lbrodie6/UofG_TDP3_TeamYes/hardware/photomasks/FRDMBoard_V2_Bottom.pdf

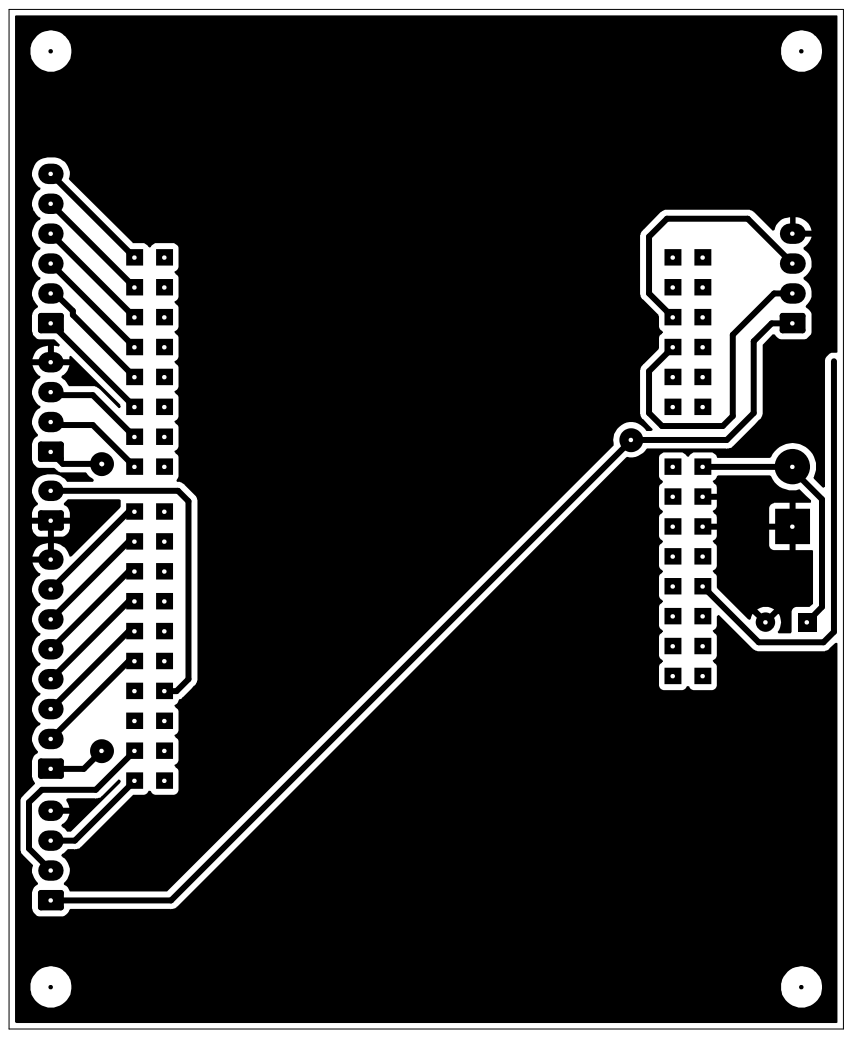
[picture p14: page 1]
