lbrodie6/UofG_TDP3_TeamYes/hardware/photomasks/FRDMBoard_V2_Top.pdf

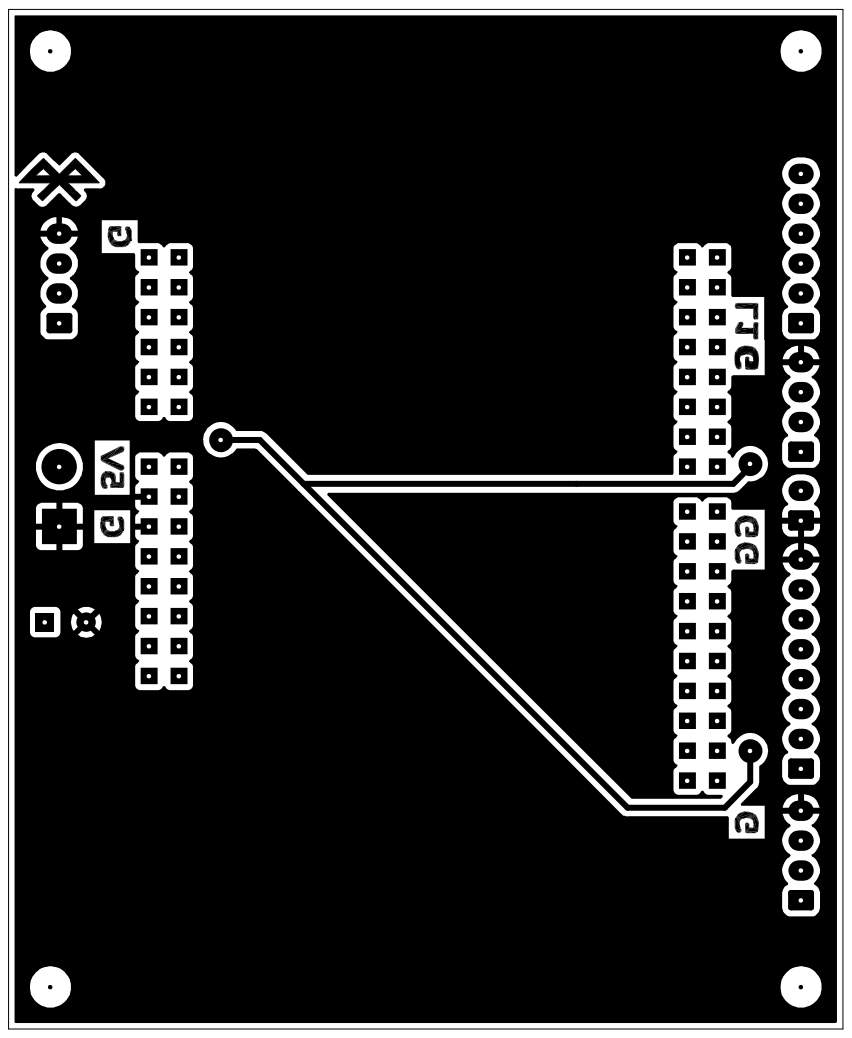
[picture p15: page 1]
