lbrodie6/UofG_TDP3_TeamYes/hardware/photomasks/ColourSensorBoard_V1_Bottom.pdf

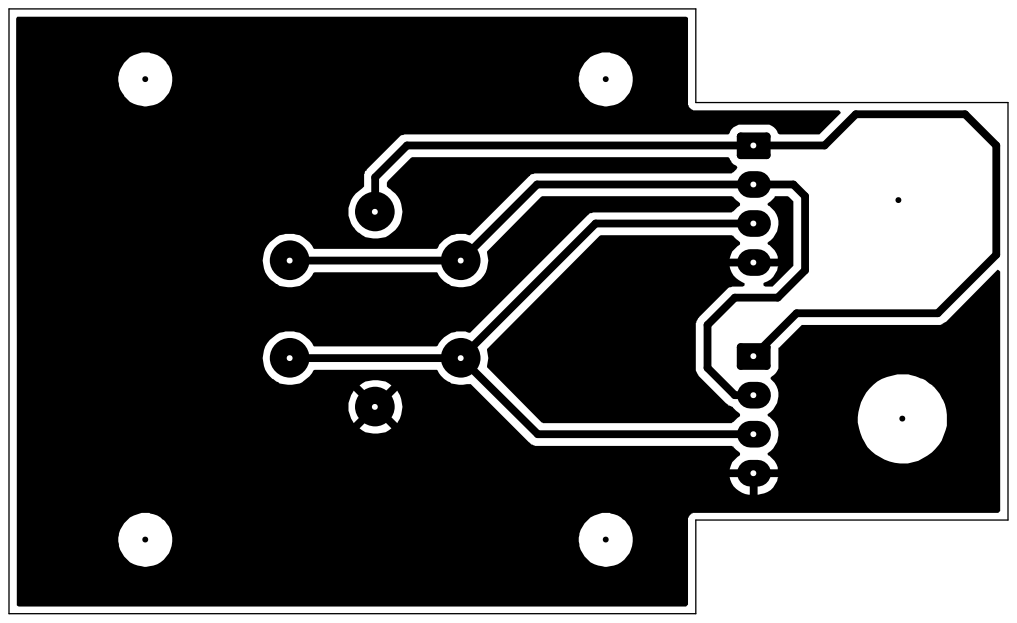
[picture p16: page 1]
