lbrodie6/UofG_TDP3_TeamYes/hardware/photomasks/ColourSensorBoard_V1_Top.pdf

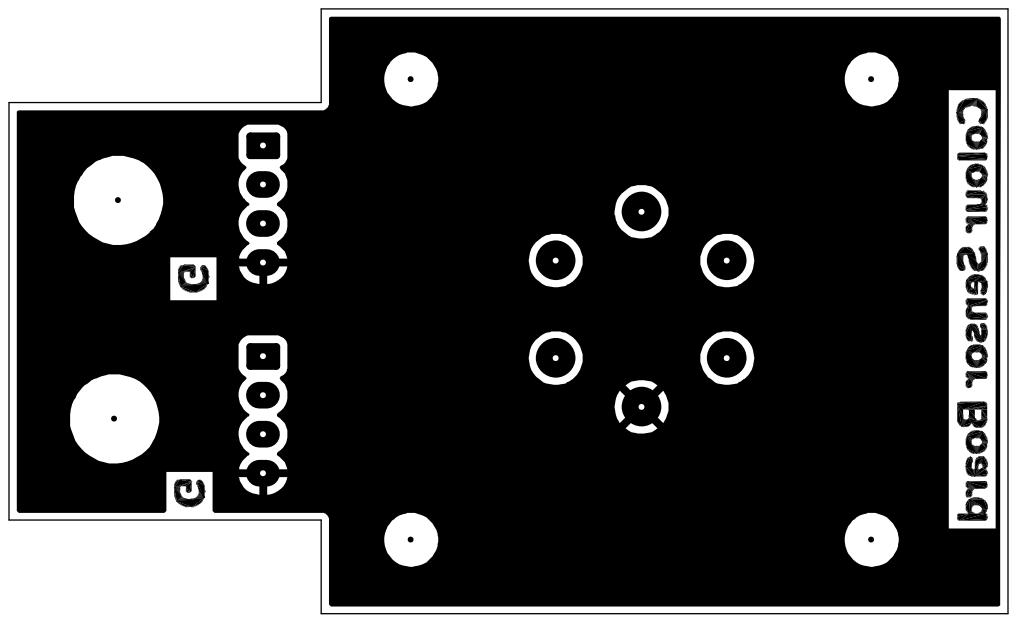
[picture p17: page 1]
