lbrodie6/UofG_TDP3_TeamYes/hardware/photomasks/FRDMBoard_V1_Bottom.pdf

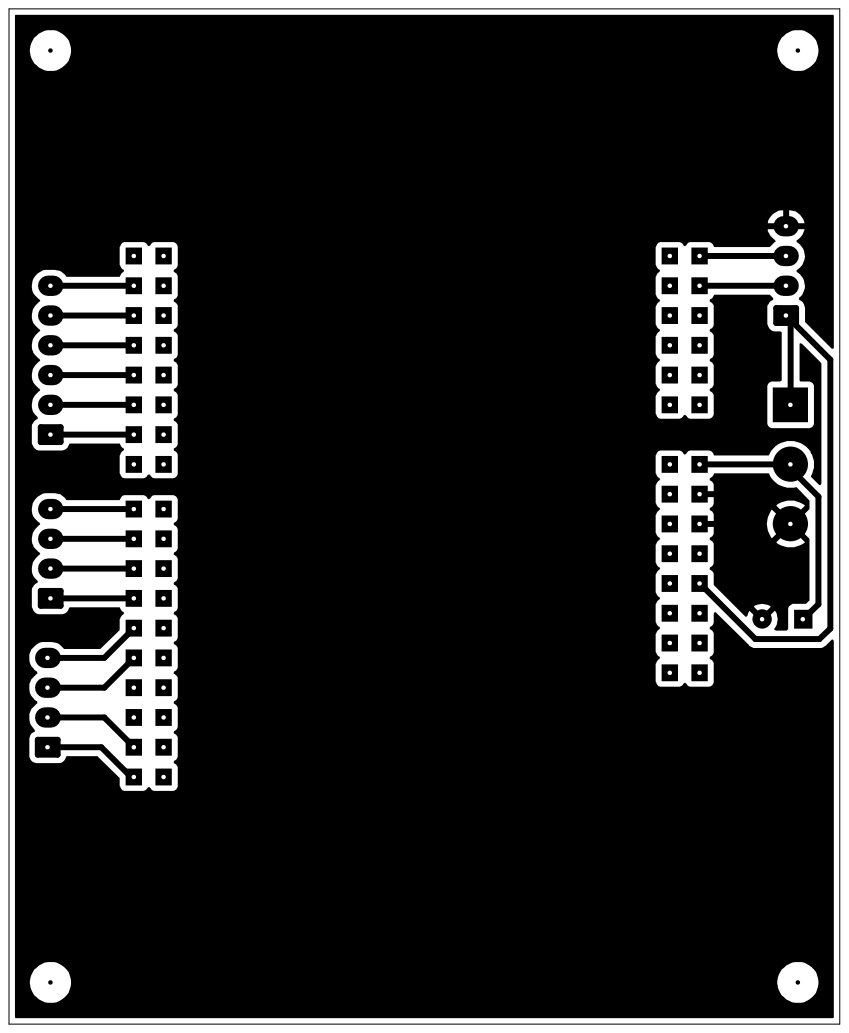
[picture p18: page 1]
