lbrodie6/UofG_TDP3_TeamYes/hardware/photomasks/FRDMBoard_V1_Top.pdf

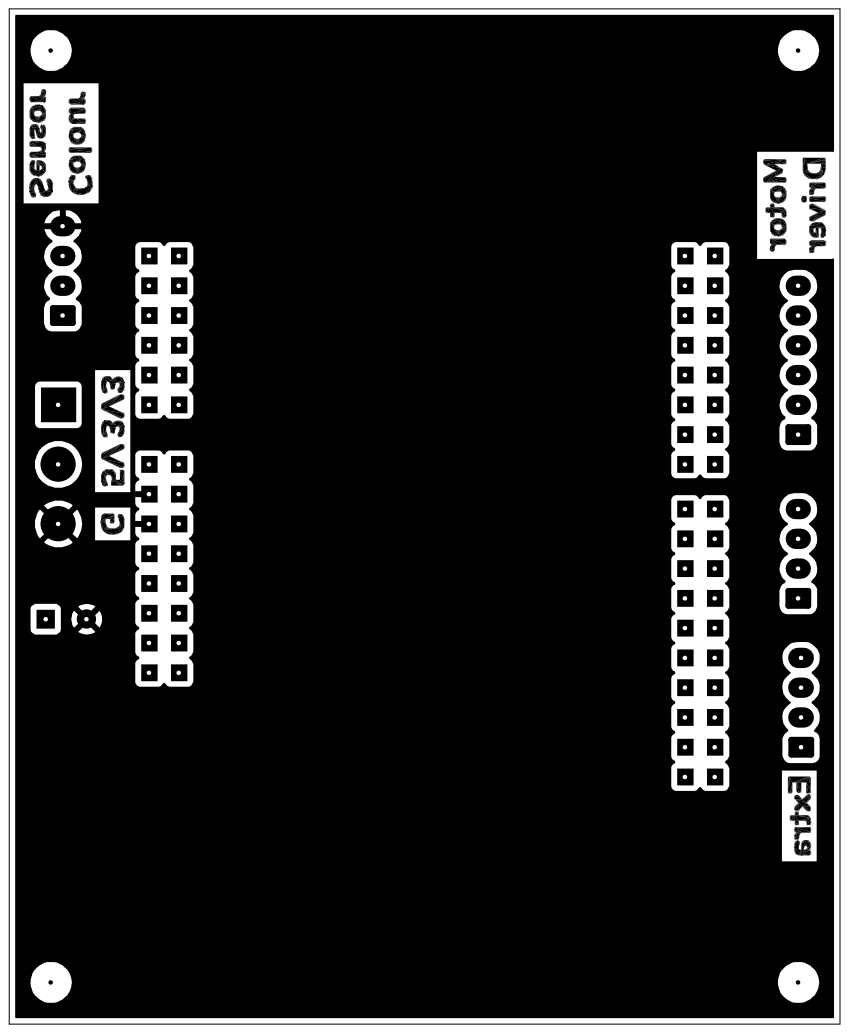
[picture p19: page 1]
