lbrodie6/UofG_TDP3_TeamYes/hardware/photomasks/MotorBoard_V1_Bottom.pdf

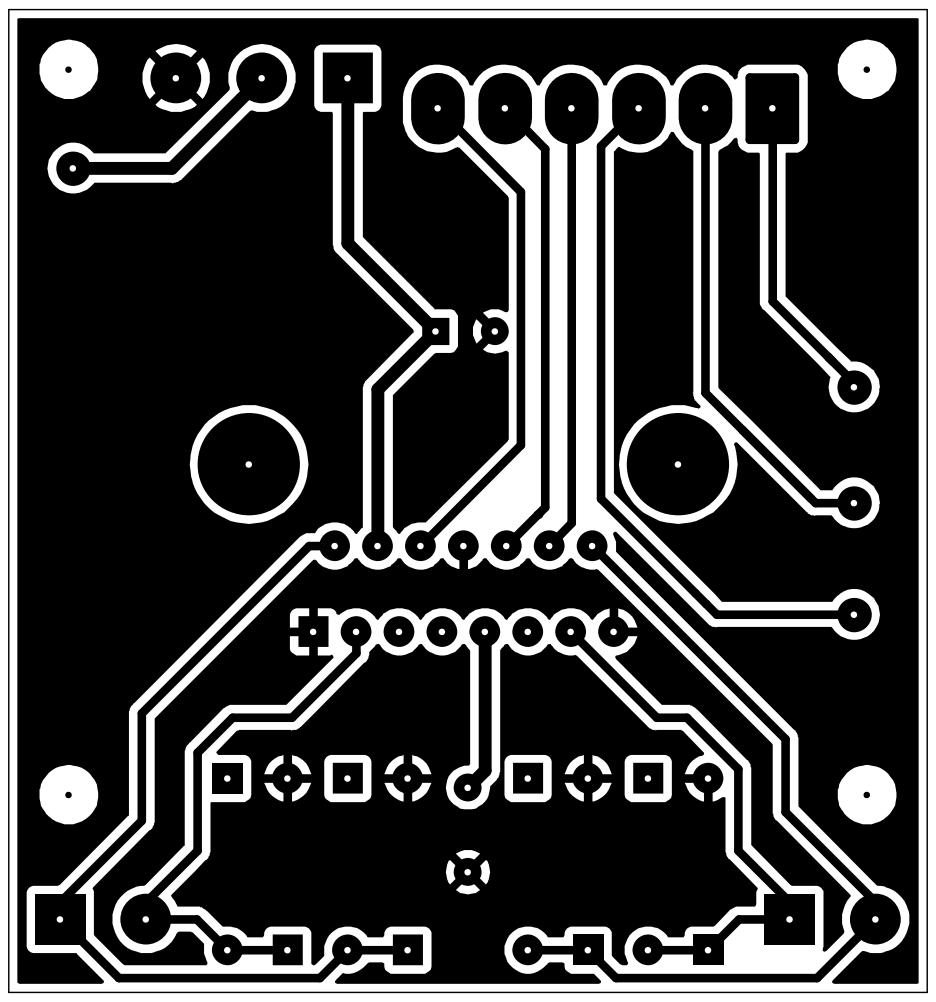
[picture p20: page 1]
