lbrodie6/UofG_TDP3_TeamYes/hardware/photomasks/MotorBoard_V1_Top.pdf

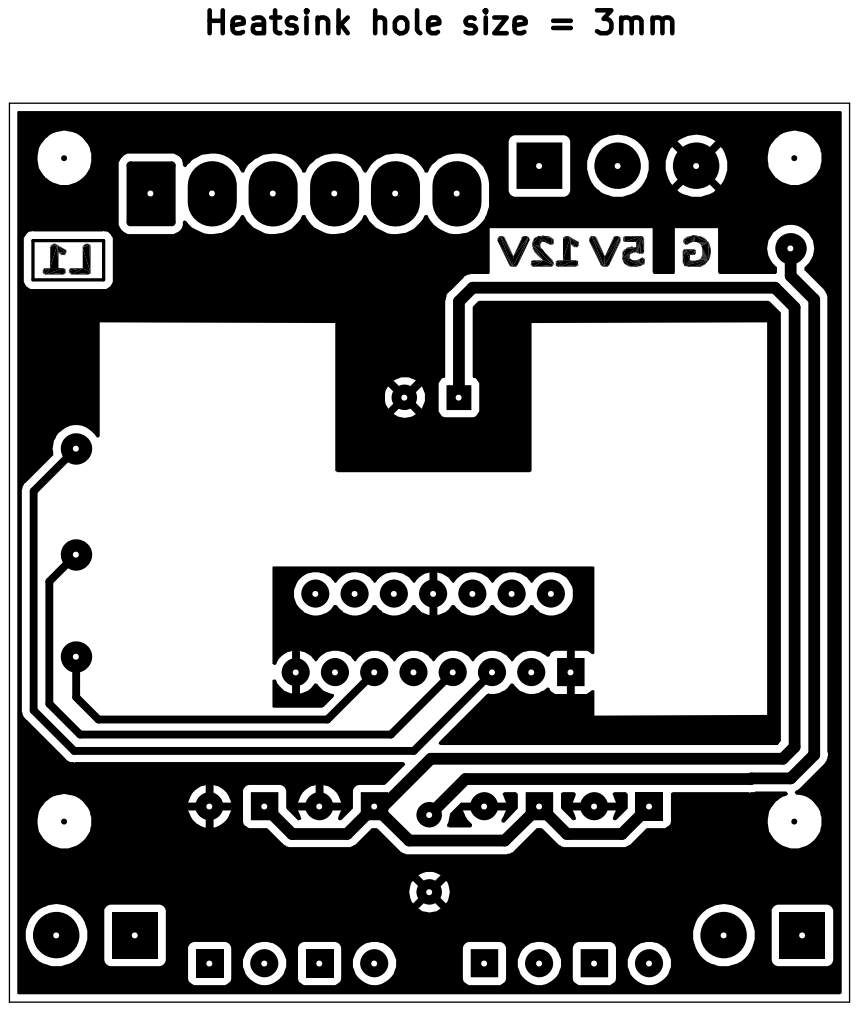
[picture p21: page 1]
