lbrodie6/UofG_TDP3_TeamYes/hardware/photomasks/PowerBoard_V1_Bottom.pdf

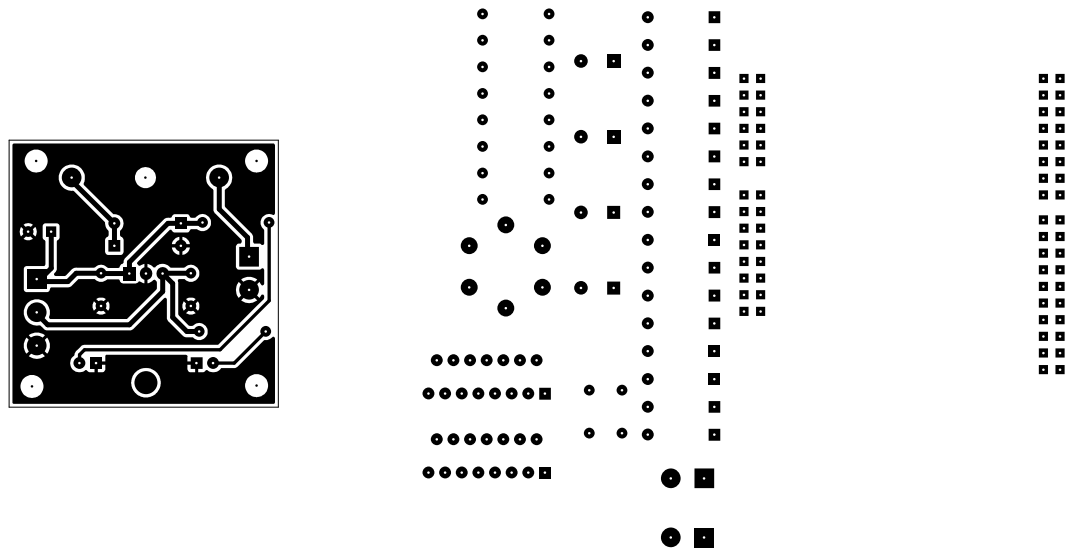
[picture p22: page 1]
