lbrodie6/UofG_TDP3_TeamYes/hardware/photomasks/PowerBoard_V1_Top.pdf

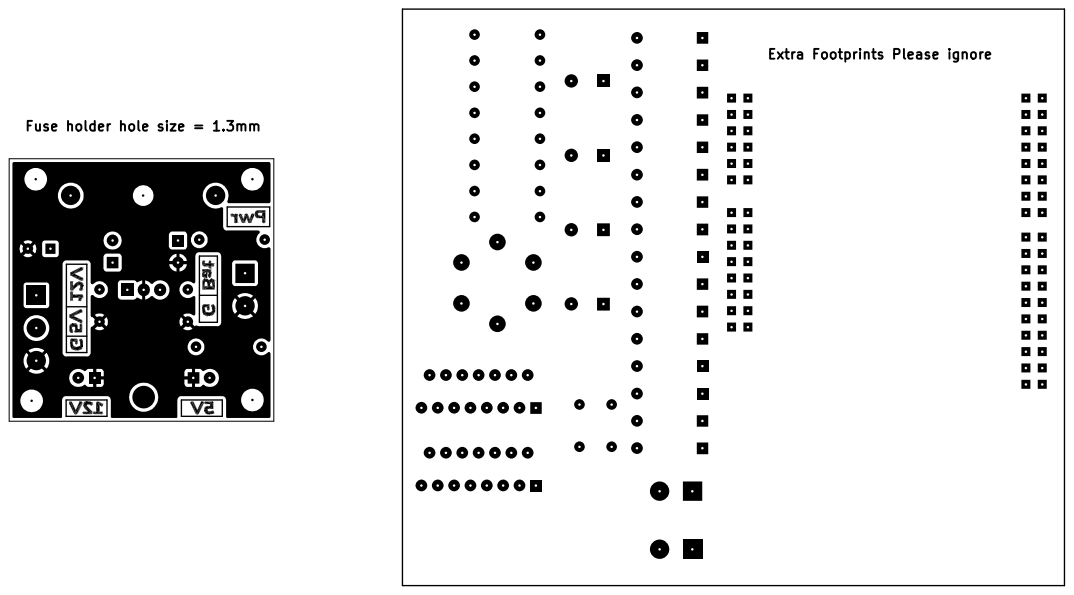
[picture p23: page 1]
